ChristianIannella/Keychain/Dice/Docs/IMG_2142.JPG

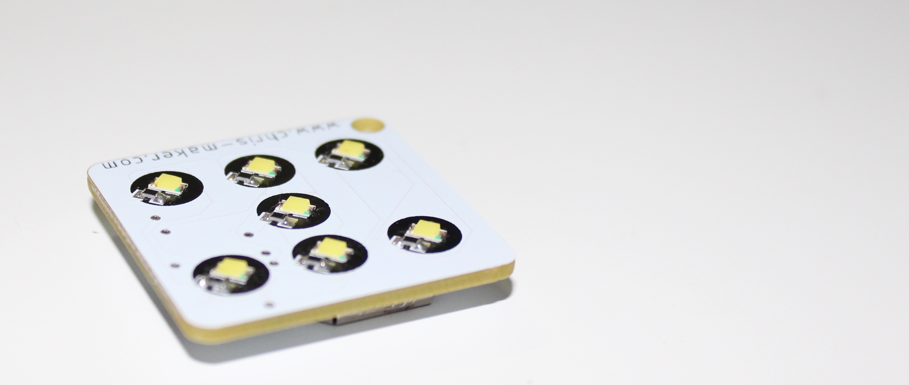
Dice/Docs/IMG_2142.JPG
