ChristianIannella/Keychain/Dice/Docs/IMG_2170.JPG

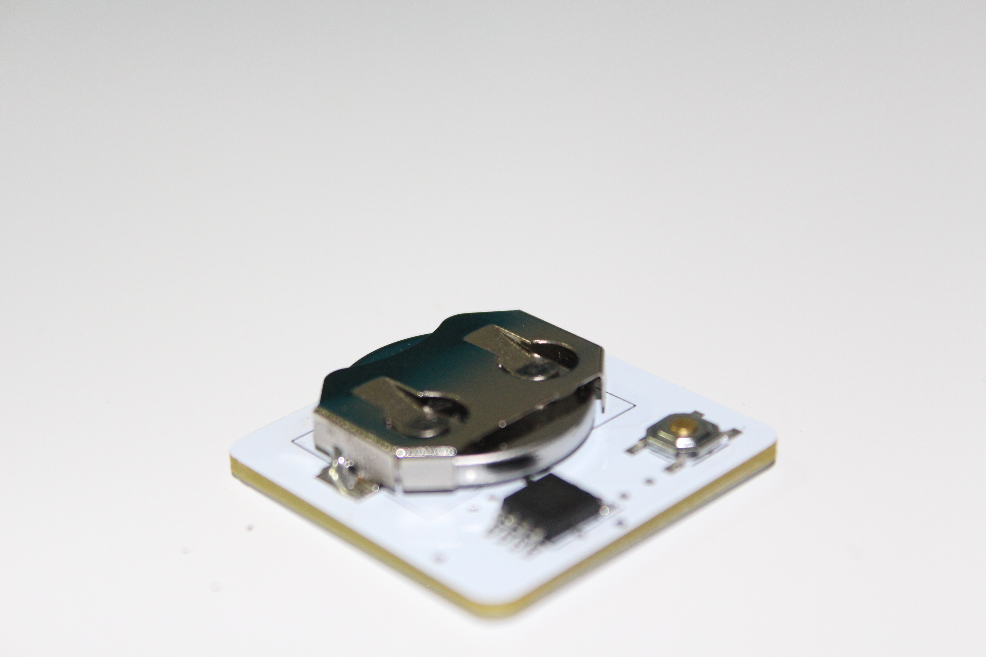
Dice/Docs/IMG_2170.JPG
